neilpat02/Electronics-Tool-Bench/Group-6/piHatTest.py

from RPi import GPIO
from time import sleep

GPIO.setwarnings(False)
GPIO.setmode(GPIO.BOARD)

GPIO.setup(3,GPIO.OUT)
GPIO.setup(5,GPIO.OUT)
GPIO.setup(7,GPIO.OUT)
GPIO.setup(8,GPIO.OUT)
GPIO.setup(10,GPIO.OUT)
GPIO.setup(11,GPIO.OUT)
GPIO.setup(12,GPIO.OUT)
GPIO.setup(13,GPIO.OUT)
GPIO.setup(15,GPIO.OUT)
GPIO.setup(16,GPIO.OUT)
GPIO.setup(18,GPIO.OUT)
GPIO.setup(19,GPIO.OUT)
GPIO.setup(21,GPIO.OUT)
GPIO.setup(22,GPIO.OUT)
GPIO.setup(23,GPIO.OUT)
GPIO.setup(24,GPIO.OUT)
GPIO.setup(26,GPIO.OUT)
#GPIO.setup(27,GPIO.OUT)
#GPIO.setup(28,GPIO.OUT)
GPIO.setup(29,GPIO.OUT)
GPIO.setup(31,GPIO.OUT)
GPIO.setup(32,GPIO.OUT)
GPIO.setup(33,GPIO.OUT)
GPIO.setup(35,GPIO.OUT)
GPIO.setup(36,GPIO.OUT)
GPIO.setup(37,GPIO.OUT)
GPIO.setup(38,GPIO.OUT)
GPIO.setup(40,GPIO.OUT)

GPIO.output(3,GPIO.LOW)
GPIO.output(5,GPIO.LOW)
GPIO.output(7,GPIO.LOW)
GPIO.output(8,GPIO.LOW)
GPIO.output(10,GPIO.LOW)
GPIO.output(11,GPIO.LOW)
GPIO.output(12,GPIO.LOW)
GPIO.output(13,GPIO.LOW)
GPIO.output(15,GPIO.LOW)
GPIO.output(16,GPIO.LOW)
GPIO.output(18,GPIO.LOW)
GPIO.output(19,GPIO.LOW)
GPIO.output(21,GPIO.LOW)
GPIO.output(22,GPIO.LOW)
GPIO.output(23,GPIO.LOW)
GPIO.output(24,GPIO.LOW)
GPIO.output(26,GPIO.LOW)
#GPIO.output(27,GPIO.LOW)
#GPIO.output(28,GPIO.LOW)
GPIO.output(29,GPIO.LOW)
GPIO.output(31,GPIO.LOW)
GPIO.output(32,GPIO.LOW)
GPIO.output(33,GPIO.LOW)
GPIO.output(35,GPIO.LOW)
GPIO.output(36,GPIO.LOW)
GPIO.output(37,GPIO.LOW)
GPIO.output(38,GPIO.LOW)
GPIO.output(40,GPIO.LOW)

d=2

while True:
    GPIO.output(3,GPIO.HIGH)
    sleep(d)
    GPIO.output(3,GPIO.LOW)
    GPIO.output(5,GPIO.HIGH)
    sleep(d)
    GPIO.output(5,GPIO.LOW)
    GPIO.output(7,GPIO.HIGH)
    sleep(d)
    GPIO.output(7,GPIO.LOW)
    GPIO.output(8,GPIO.HIGH)
    sleep(d)
    GPIO.output(8,GPIO.LOW)
    GPIO.output(10,GPIO.HIGH)
    sleep(d)
    GPIO.output(10,GPIO.LOW)
    GPIO.output(11,GPIO.HIGH)
    sleep(d)
    GPIO.output(11,GPIO.LOW)
    GPIO.output(12,GPIO.HIGH)
    sleep(d)
    GPIO.output(12,GPIO.LOW)
    GPIO.output(13,GPIO.HIGH)
    sleep(d)
    GPIO.output(13,GPIO.LOW)
    GPIO.output(15,GPIO.HIGH)
    sleep(d)
    GPIO.output(15,GPIO.LOW)
    GPIO.output(16,GPIO.HIGH)
    sleep(d)
    GPIO.output(16,GPIO.LOW)
    GPIO.output(18,GPIO.HIGH)
    sleep(d)
    GPIO.output(18,GPIO.LOW)
    GPIO.output(19,GPIO.HIGH)
    sleep(d)
    GPIO.output(19,GPIO.LOW)
    GPIO.output(21,GPIO.HIGH)
    sleep(d)
    GPIO.output(21,GPIO.LOW)
    GPIO.output(22,GPIO.HIGH)
    sleep(d)
    GPIO.output(22,GPIO.LOW)
    GPIO.output(23,GPIO.HIGH)
    sleep(d)
    GPIO.output(23,GPIO.LOW)
    GPIO.output(24,GPIO.HIGH)
    sleep(d)
    GPIO.output(24,GPIO.LOW)
    GPIO.output(26,GPIO.HIGH)
    sleep(d)
    GPIO.output(26,GPIO.LOW)
   #GPIO.output(27,GPIO.HIGH)
    #sleep(d)
    #GPIO.output(27,GPIO.LOW)
    #GPIO.output(28,GPIO.HIGH)
    #sleep(d)
    #GPIO.output(28,GPIO.LOW)
    GPIO.output(29,GPIO.HIGH)
    sleep(d)
    GPIO.output(29,GPIO.LOW)
    GPIO.output(31,GPIO.HIGH)
    sleep(d)
    GPIO.output(31,GPIO.LOW)
    GPIO.output(32,GPIO.HIGH)
    sleep(d)
    GPIO.output(32,GPIO.LOW)
    GPIO.output(33,GPIO.HIGH)
    sleep(d)
    GPIO.output(33,GPIO.LOW)
    GPIO.output(35,GPIO.HIGH)
    sleep(d)
    GPIO.output(35,GPIO.LOW)
    GPIO.output(36,GPIO.HIGH)
    sleep(d)
    GPIO.output(36,GPIO.LOW)
    GPIO.output(37,GPIO.HIGH)
    sleep(d)
    GPIO.output(37,GPIO.LOW)
    GPIO.output(38,GPIO.HIGH)
    sleep(d)
    GPIO.output(38,GPIO.LOW)
    GPIO.output(40,GPIO.HIGH)
    sleep(d)
    GPIO.output(40,GPIO.LOW)
